JonkiTroll/Rover/Snow+Tank+from+RCTESTFLIGHT/images/1.jpg

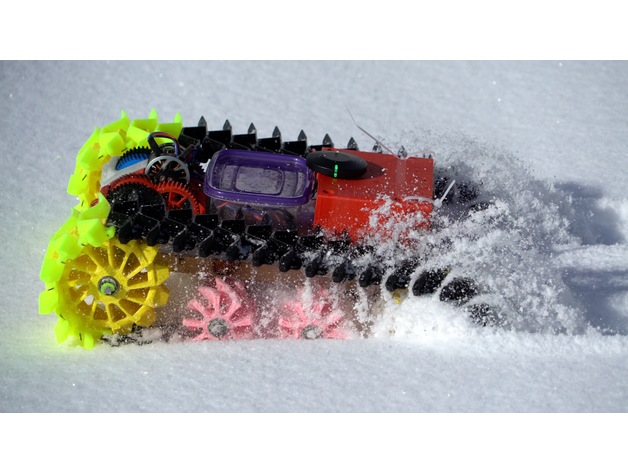
Snow+Tank+from+RCTESTFLIGHT/images/1.jpg
