JonkiTroll/Rover/Snow+Tank+from+RCTESTFLIGHT/images/2.jpg

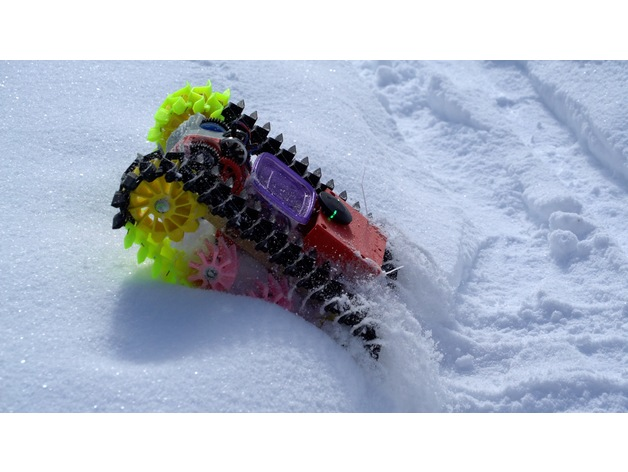
Snow+Tank+from+RCTESTFLIGHT/images/2.jpg
