JonkiTroll/Rover/Snow+Tank+from+RCTESTFLIGHT/images/3.jpg

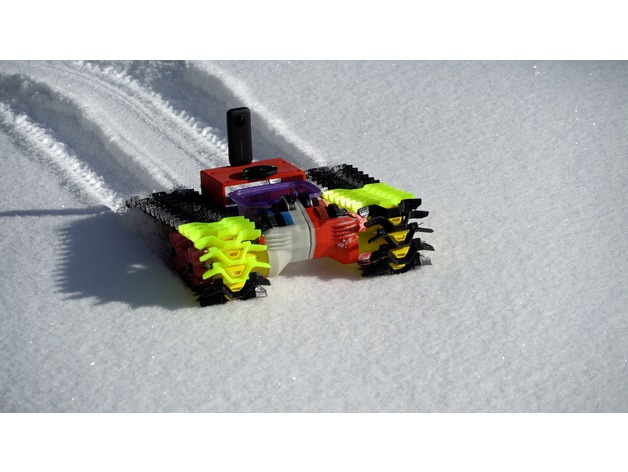
Snow+Tank+from+RCTESTFLIGHT/images/3.jpg
