JonkiTroll/Rover/Snow+Tank+from+RCTESTFLIGHT/images/8mm_Tube_Clamp.png

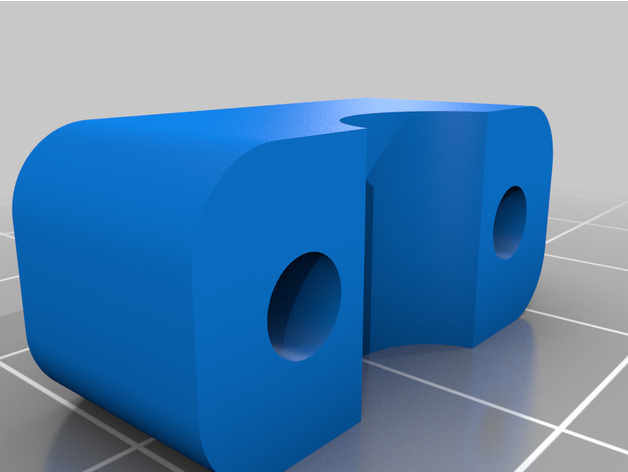
Snow+Tank+from+RCTESTFLIGHT/images/8mm_Tube_Clamp.png
