JonkiTroll/Rover/Snow+Tank+from+RCTESTFLIGHT/images/40T.png

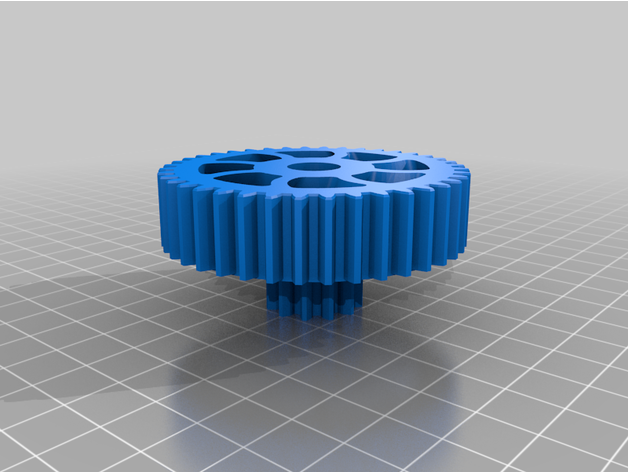
Snow+Tank+from+RCTESTFLIGHT/images/40T.png
