JonkiTroll/Rover/Snow+Tank+from+RCTESTFLIGHT/images/56_to_1_housing.png

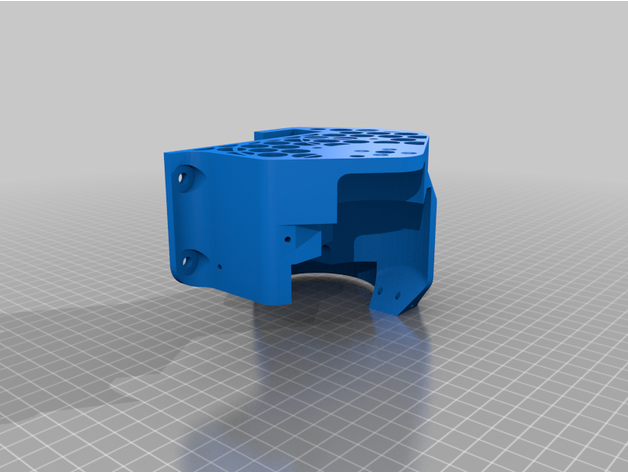
Snow+Tank+from+RCTESTFLIGHT/images/56_to_1_housing.png
