JonkiTroll/Rover/Snow+Tank+from+RCTESTFLIGHT/images/82mm_Idler_Wheel.png

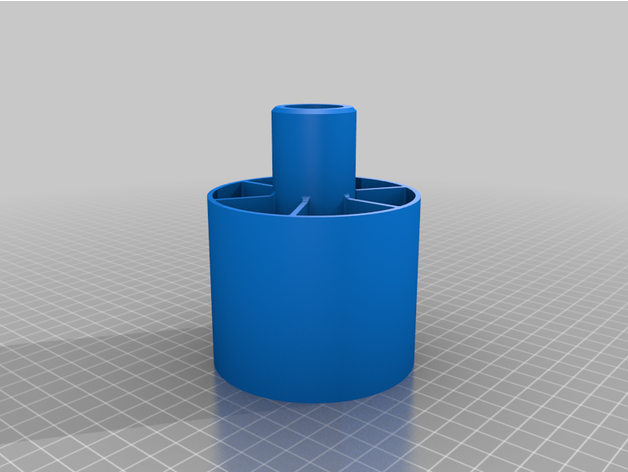
Snow+Tank+from+RCTESTFLIGHT/images/82mm_Idler_Wheel.png
