JonkiTroll/Rover/Snow+Tank+from+RCTESTFLIGHT/images/Corner_Axel_Holder_for_skids_only.png

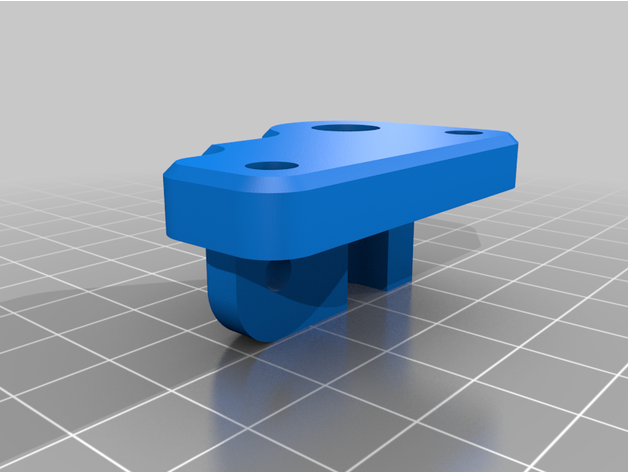
Snow+Tank+from+RCTESTFLIGHT/images/Corner_Axel_Holder_for_skids_only.png
