JonkiTroll/Rover/Snow+Tank+from+RCTESTFLIGHT/images/Rear_Axel_Holder.png

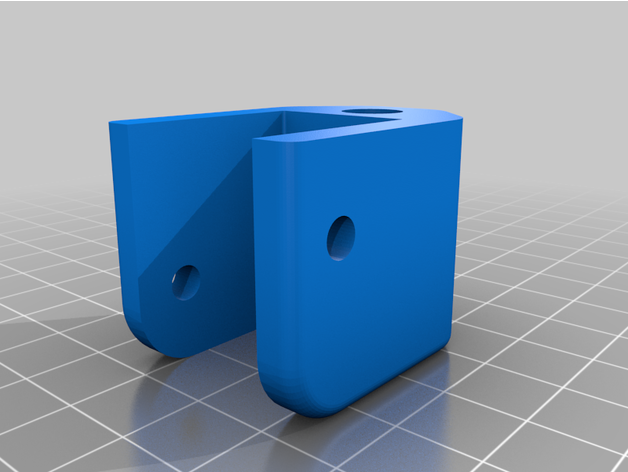
Snow+Tank+from+RCTESTFLIGHT/images/Rear_Axel_Holder.png
