JonkiTroll/Rover/Snow+Tank+from+RCTESTFLIGHT/images/Screen_Shot_2020-04-23_at_10.11.50_AM.png

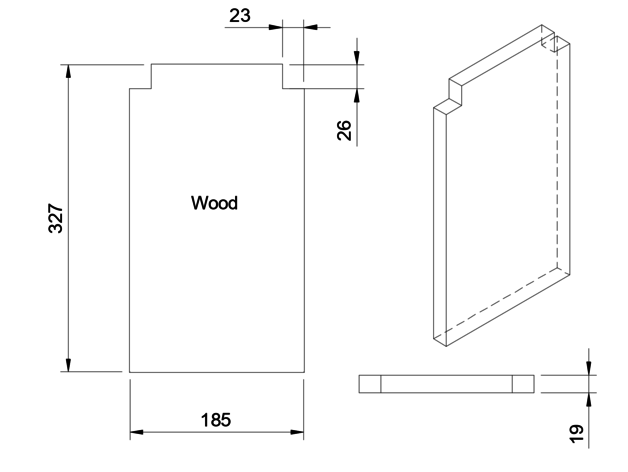
Snow+Tank+from+RCTESTFLIGHT/images/Screen_Shot_2020-04-23_at_10.11.50_AM.png
