JonkiTroll/Rover/Snow+Tank+from+RCTESTFLIGHT/images/Simple_Top_Box.png

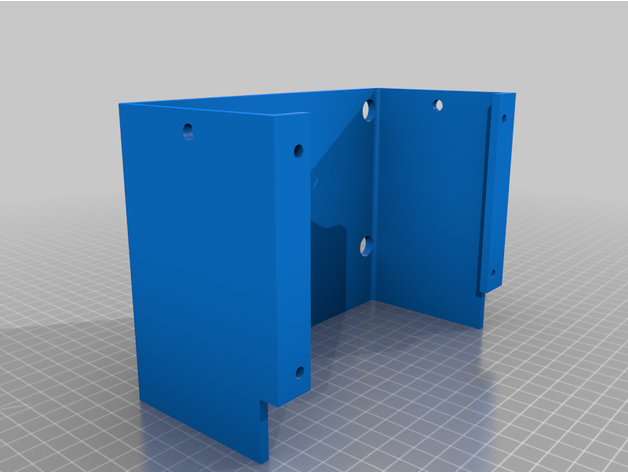
Snow+Tank+from+RCTESTFLIGHT/images/Simple_Top_Box.png
