JonkiTroll/Rover/Snow+Tank+from+RCTESTFLIGHT/images/Skid.png

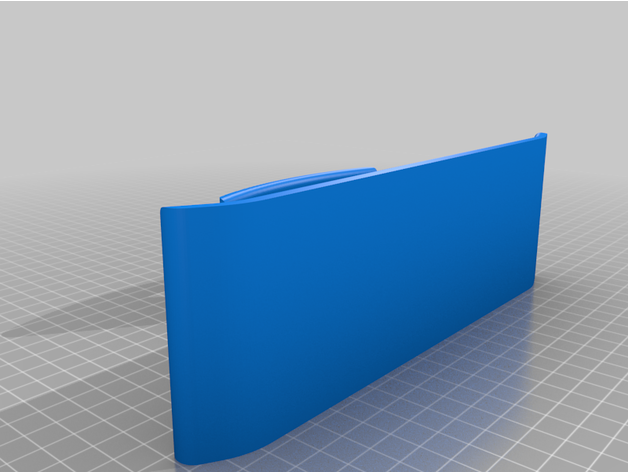
Snow+Tank+from+RCTESTFLIGHT/images/Skid.png
