JonkiTroll/Rover/Snow+Tank+from+RCTESTFLIGHT/images/Snow_Pully_Rear.png

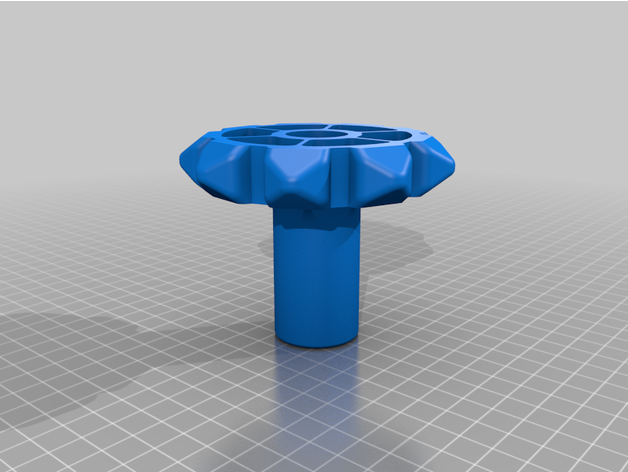
Snow+Tank+from+RCTESTFLIGHT/images/Snow_Pully_Rear.png
