JonkiTroll/Rover/Snow+Tank+from+RCTESTFLIGHT/images/Snow_Track.png

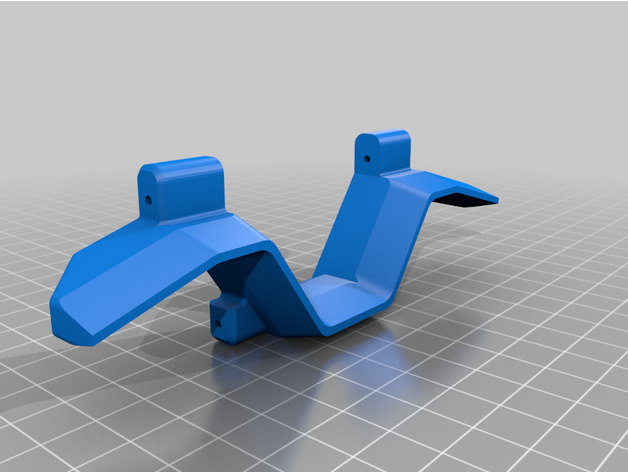
Snow+Tank+from+RCTESTFLIGHT/images/Snow_Track.png
