JonkiTroll/Rover/Snow+Tank+from+RCTESTFLIGHT/files/Skid_Leg.stl

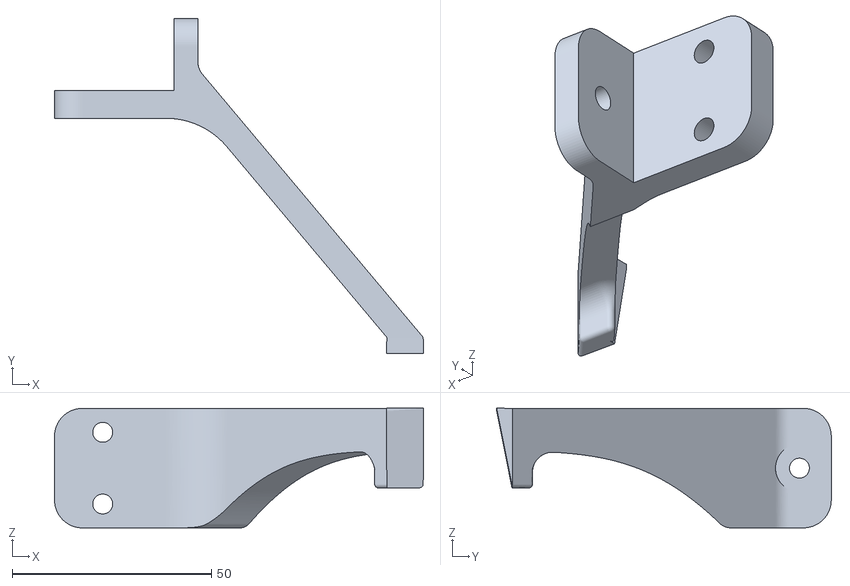
[picture p33: CAD file, 2021-01-31]
Snow+Tank+from+RCTESTFLIGHT/files/Skid_Leg.stl
92.6 x 84.0 x 30.1
