JonkiTroll/Rover/Snow+Tank+from+RCTESTFLIGHT/files/Rear_Axel_Holder.STL

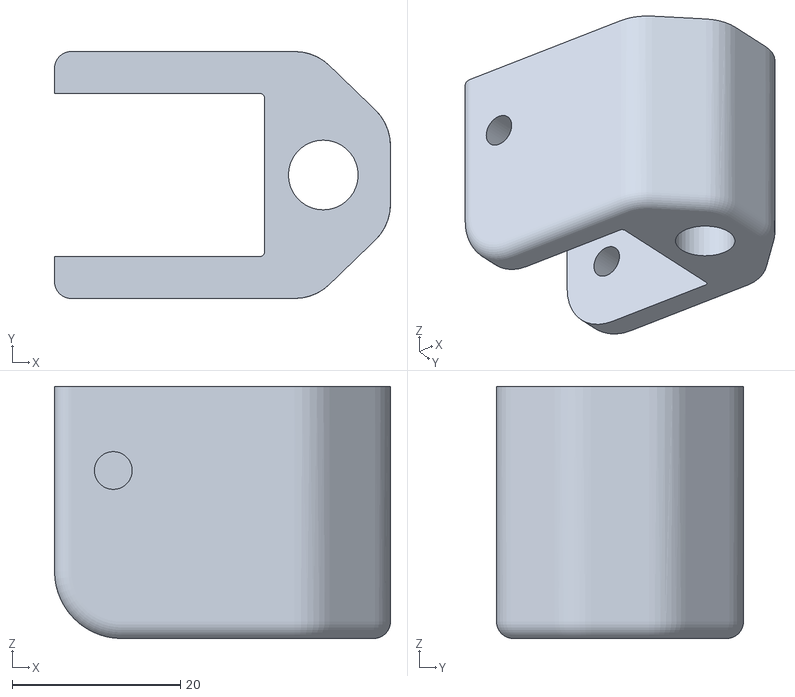
[picture p34: CAD file, 2021-01-31]
Snow+Tank+from+RCTESTFLIGHT/files/Rear_Axel_Holder.STL
40.0 x 29.4 x 30.0
