JonkiTroll/Rover/Snow+Tank+from+RCTESTFLIGHT/files/40T.STL

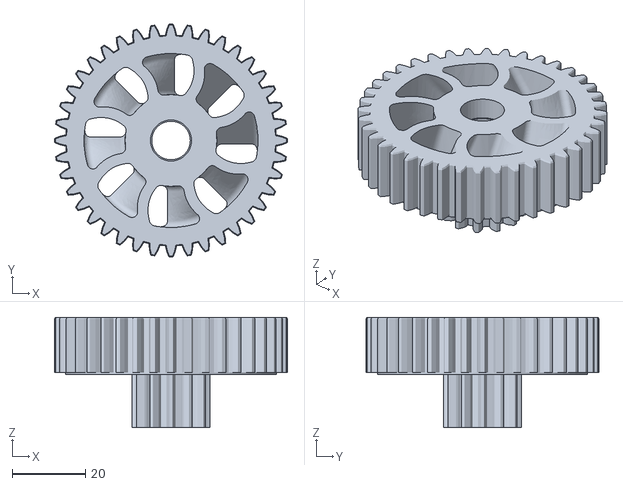
[picture p35: CAD file, 2021-01-31]
Snow+Tank+from+RCTESTFLIGHT/files/40T.STL
63.5 x 63.5 x 30.0
